ErikJohnsonCU/Tesa/Hardware/Analog Design/commSystemDesign.asc

C1: cap; 4.7µ
C2: cap; 4.7µ
C3: cap; 4.7µ
D1: diode
D2: diode
R1: res; 100
R2: res; 470
R3: res; 470
R4: res; 530
R5: res; 12k
R6: res; 100
U1: LT1366
V1: voltage; PULSE(0 5 0 0.000000000000001 0.000000000000001 0.010 0.020 10)
V2: voltage; 12
V3: voltage; 3.3
Named nets: 0
.tran 0.10 uic
